Fiborn/fibocom-iot-2026--2.0--/ESP32-P4_Function_EV_Board/main/challenge_anim/frame_0145.jpg

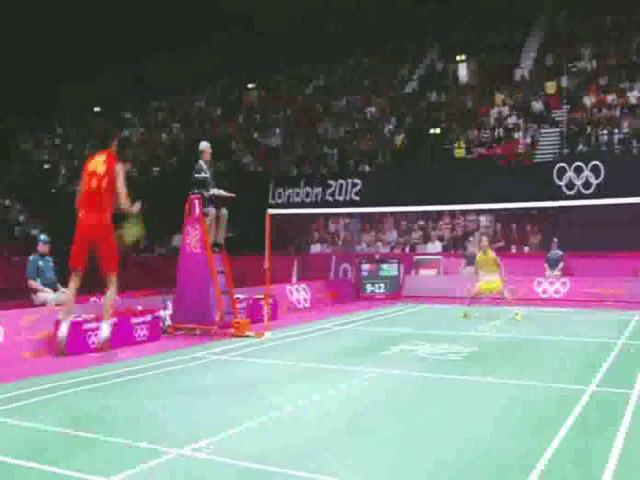
ESP32-P4_Function_EV_Board/main/challenge_anim/frame_0145.jpg
