Fiborn/fibocom-iot-2026--2.0--/Sunplus_Camera/lensesca_model.jpg

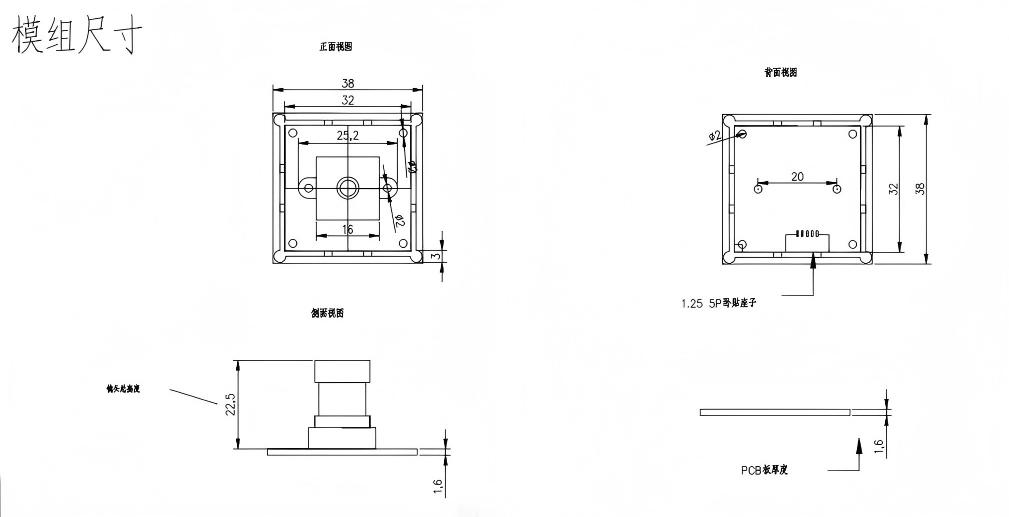
Sunplus_Camera/lensesca_model.jpg
