Fiborn/fibocom-iot-2026--2.0--/Aliyun/court/src/shader.cpp

#include "shader.h"
#include <iostream>

Shader::~Shader() {
    if (program) glDeleteProgram(program);
}

GLuint Shader::compileShader(GLenum type, const std::string& source) {
    GLuint shader = glCreateShader(type);
    const char* src = source.c_str();
    glShaderSource(shader, 1, &src, nullptr);
    glCompileShader(shader);

    GLint success;
    glGetShaderiv(shader, GL_COMPILE_STATUS, &success);
    if (!success) {
        char info[512];
        glGetShaderInfoLog(shader, 512, nullptr, info);
        std::cerr << "Shader compile error (" << (type == GL_VERTEX_SHADER ? "VERT" : "FRAG") << "):\n" << info << std::endl;
    }
    return shader;
}

bool Shader::loadFromStrings(const std::string& vertexSource,
                              const std::string& fragmentSource) {
    GLuint vs = compileShader(GL_VERTEX_SHADER, vertexSource);
    GLuint fs = compileShader(GL_FRAGMENT_SHADER, fragmentSource);

    program = glCreateProgram();
    glAttachShader(program, vs);
    glAttachShader(program, fs);
    glLinkProgram(program);

    GLint success;
    glGetProgramiv(program, GL_LINK_STATUS, &success);
    if (!success) {
        char info[512];
        glGetProgramInfoLog(program, 512, nullptr, info);
        std::cerr << "Program link error:\n" << info << std::endl;
        return false;
    }

    glDeleteShader(vs);
    glDeleteShader(fs);
    return true;
}

void Shader::use() const { glUseProgram(program); }

void Shader::setMat4(const std::string& name, const glm::mat4& mat) const {
    glUniformMatrix4fv(glGetUniformLocation(program, name.c_str()), 1, GL_FALSE, &mat[0][0]);
}

void Shader::setVec3(const std::string& name, const glm::vec3& vec) const {
    glUniform3fv(glGetUniformLocation(program, name.c_str()), 1, &vec[0]);
}

void Shader::setFloat(const std::string& name, float value) const {
    glUniform1f(glGetUniformLocation(program, name.c_str()), value);
}

void Shader::setInt(const std::string& name, int value) const {
    glUniform1i(glGetUniformLocation(program, name.c_str()), value);
}
